GregT7/NetraPi/project_management/specs/test_matrix.xlsx

Sheet: tp
test_number | test_name | description | status
TP-01 | Budget compliance check | Verifies the total NetraPi system cost remains within the allowed budget. | PASS
TP-02 | Picam smoke test | Verifies the Raspberry Pi detects the camera and can display clear live output. | PASS
TP-03 | Portable-battery-only power verification | Verifies the Raspberry Pi can boot and operate using only the portable battery. | PASS
TP-04 | Camera mounting verification | Verifies the camera is mounted securely and provides a stable, usable forward-facing view during driving. | PASS
TP-05 | Vehicle compatibility inspection | Verifies the planned hardware can be installed and operated within a 2010 Mazda3 sedan. | PASS
TP-06 | Safety and legality review | Verifies the installed system does not obviously violate safety or driving constraints. | PASS
TP-07 | Reversible removal verification | Verifies the Pi, TPU, and battery can be removed and reinstalled without permanent modification or damage. | PASS
TP-08 | Three-hour continuous recording to memory | Verifies the system continuously records and writes footage to memory for at least 3 hours. | PASS
TP-09 | Texas-summer supervised operation check | Verifies the system can operate under typical Texas summer temperatures with supervision. | PASS
TP-10 | Coral TPU smoke test | Verifies the Coral USB TPU is detected and usable on the Raspberry Pi. | PASS
TP-11 | AI inference smoke test (camera + TPU) | Verifies real-time inference runs on live camera feed with object detection output. | PASS
TP-11.5 | Live inference pipeline throughput and latency benchmark | Measures the performance of the live camera-to-TPU inference pipeline, including effective FPS, processing latency, and identification of system bottlenecks. | PASS
TP-12 | Detection loop real-time operation | Verifies continuous inference execution without crashes or stalls. | PASS
TP-13 | Capture configuration validation | Verifies resolution, frame rate, and buffer duration are configurable and applied correctly. | PASS
TP-14 | Rolling buffer and event clip extraction verification | Verifies rolling buffer and event-triggered clip generation produce correct pre/post coverage. | PASS
TP-15 | Speaker module feedback verification | Verifies the speaker module produces audible feedback suitable for in-vehicle use. | PASS
TP-16 | Event clip pipeline and project layout | Verifies the event/clip pipeline is documented and the repo layout matches the planned `src/` structure for the edge capture path (no DB or cloud wiring required). | PASS
TP-17 | Config loading unit verification | Verifies JSON config files load into typed config objects used by capture and detector modules. | PASS
TP-18 | Detector data model and unit tests | Verifies `Classification`, `FrameRecord`, `FrameBuffer`, and `DetectorConfig` behave per the pipeline design. | PASS
TP-19 | Detector inference unit tests (mocked TPU) | Verifies `Detector.classify(raw)` wiring with mocked `_invoke` (no Coral required). | PASS
TP-20 | Detector on-device smoke | Verifies `load()`, `verify_tpu()`, and one real `classify(raw)` on the Pi with Coral attached. | PASS
TP-21 | RecordingManager capture unit tests | Verifies capture-related classes (`Camera`, `FrameProcessor`, `FrameRecord`, `FrameBuffer`, `Recorder`, `ClipPackage`, `PreviewUI`, etc.) pass unit tests and live under the planned `src/` layout. | PASS
TP-22 | RecordingManager idle run loop integration | Verifies `run_loop()` idle path: camera → `FrameRecord` → `pre_buffer.push` with stub config and without requiring unsafe-event logic. | PASS
TP-23 | RecordingManager clip-active path and MP4 output | Verifies `clip_active` post-roll, `ClipPackage.build`, and `Recorder.write_clip` produce a playable MP4 from buffer `display` frames. | PASS
TP-24 | RecordingManager Ctrl+C and preview controls | Verifies clean shutdown on Ctrl+C and preview show/hide per config. | PASS
AT-2.1 | Recorder write failure and recovery | Verifies `RecordingManager` handles `Recorder.write_clip(...)` failures safely (writer open fail, mid-write exception, output path issue) and recovers for subsequent clips. | PASS
AT-2.2 | Event gate policy matrix (unsafe vs safe) | Verifies clip-start policy exactly matches design: unsafe events always record; safe events record only when `record_safe_events = true`. | PASS
AT-2.3 | Post-roll completion boundary precision | Verifies post-roll finalization gate is correct at threshold boundaries (`min_post_frames_for_fps`) and avoids off-by-one behavior. | PASS
AT-2.4 | Deterministic preview-to-file parity | Verifies `PreviewUI` and saved MP4 carry the same processed `display` frames using deterministic frame markers (not subjective visual comparison). | PASS
AT-2.5 | Long-run multi-cycle stability and resource hygiene | Verifies repeated `idle -> clip_active -> idle` cycles remain stable over an extended run without state/resource leakage. | PASS
TP-25 | Stop-sign event classification (recorded clips) | Verifies classification on ~100 labeled clips (~25 each: rolling stop, run-through, complete stop, no event); overall accuracy ≥ 75%; per-category counts recorded. | PASS
TP-26 | Unsafe event clip extraction for stop-sign violation | Verifies an evidence clip is saved for an unsafe stop-sign event (rolling stop or run-through) and includes the encounter footage. | PASS
TP-27 | Audible feedback on unsafe stop-sign event | Verifies audible feedback for rolling-stop and run-through events within 10 seconds of detection. | PASS
TP-28 | Stop-sign beep test (in-vehicle) | Verifies in-car speaker beeps (3× 1.5s) when approaching three different stop signs. | PASS
AT-3.1 | Buzzer secured in Pi enclosure (GPIO wiring) | Buzzer mounted and wired safely in the Pi enclosure (BCM 18). | PASS
AT-3.3 | Continuous approach live benchmark (Pi FPS + overlay) | Live approach path meets FPS/latency targets; approach visible on HDMI. | PASS
AT-3.4 | Live approach + motion + classification bench (Pi) | Pi soak: approach + 5s motion + two-stage kNN; one cycle per maneuver; timing/FPS OK. | PASS
TP-29 | Local database schema validation | Verifies the local SQLite schema is structured correctly for event metadata storage (no upload-queue tables). | PASS
TP-30 | Local database write/read smoke test | Verifies the application can persist and retrieve dummy event records from SQLite. | PASS
TP-31 | Event metadata local storage verification | Verifies unsafe stop-sign events are stored in SQLite with required metadata. | PASS
TP-32 | Private S3 bucket provisioning | Verifies a private AWS S3 bucket exists for NetraPi media. | PASS
TP-33 | Supabase project and Postgres connectivity | Verifies the Supabase (Postgres) project exists and accepts connections from the development machine (admin / psql / SQL editor). This is not the FastAPI app connecting. | PASS
TP-34 | Local FastAPI smoke insert (driving-session) | Verifies a local FastAPI app (uvicorn, not Docker) can POST /api/netrapi/driving-session and insert one SQLite row. JSON only — no file body. | PASS
TP-35 | Local FastAPI health | Verifies GET /health on the local uvicorn app returns liveness and a UTC timestamp. No API key. | PASS
TP-36 | Local FastAPI smoke insert (driving-event) | Verifies POST /api/netrapi/driving-event on local uvicorn inserts one event plus nested children into SQLite (clip local flags, auto classification). JSON only — no file body. | PASS
TP-37 | Local backend boots via Docker Compose | Verifies the local FastAPI backend starts from the repo’s local Docker / Compose setup. | PASS
TP-38 | Local backend can reach S3 | Verifies the local backend process is configured with AWS credentials and can write a small test object to the private bucket. | PASS
TP-39 | Local backend can reach Supabase | Verifies the local backend can open a Postgres session to Supabase using its configured credentials. | PASS
TP-40 | Cloud metadata schema deployment | Verifies the event-metadata schema is applied to Supabase Postgres from the running local backend. | PASS
TP-41 | Trip-segment local insert | Verifies full-session trip recording writes at least one trip_segment row with a local MP4 path after the loop stops. | PASS
TP-42 | Edge API-key authentication | Verifies the local backend authenticates edge clients with an API key and rejects unauthenticated requests. | PASS
TP-43 | s3-upload-url issuance and edge PUT | Verifies POST /api/netrapi/s3-upload-url (JSON only) returns a time-limited S3 PUT URL and object key and the client PUTs bytes to S3 not to FastAPI. | PASS
TP-44 | Stable S3 object key generation | Verifies the backend assigns consistent deterministic object keys. | PASS
TP-45 | driving-event persist to Supabase | Verifies authenticated POST /api/netrapi/driving-event writes one event plus nested children to Postgres. JSON only. Cloud counterpart of TP-36. | PASS
TP-46 | Private object access via signed GET | Ensures uploaded objects are not public and are reachable via backend-issued signed GET URLs (POST /api/netrapi/s3-download-url). | PASS
TP-47 | confirm-s3-upload links S3 object to Postgres | Verifies POST /api/netrapi/confirm-s3-upload (JSON only) sets s3_key / s3_stored after the edge PUT in TP-43. | PASS
TP-48 | Presigned upload over hotspot/mobile data | Verifies an edge client can complete a backend-orchestrated upload over cellular/hotspot connectivity. | PASS
TP-49 | Local end-to-end event persistence via backend | Verifies a local event (SQLite plus clip) uploads one-at-a-time through the local backend into S3 and Postgres. | PASS
TP-50 | Backend Docker image build | Verifies the backend Docker image builds and runs locally from the production Dockerfile. | PASS
TP-51 | Backend deployment to hosting environment | Verifies the backend deploys successfully to the target host (e.g., Render). | PASS
TP-52 | Deployed backend API-key authentication | Verifies the deployed backend authenticates edge clients with an API key, rejects unauthenticated requests, and still accepts a valid key (same contract as local TP-42). | PASS
TP-53 | Unsafe event to cloud via deployed backend | Verifies an unsafe stop-sign event is detected on the edge, alerts locally, and uploads through the deployed backend to S3 + Postgres. | PASS
TP-54 | Cross-layer metadata consistency | Verifies event identity and fields stay consistent across the TP-53 SQLite artifact (session / event / clip / trip / s3_key) after a successful CloudIngest confirm (no frontend; no backend .env on the Pi). | PASS
TP-55 | Restart recovery then upload | Verifies local event data survives an edge restart and can upload later via the deployed backend. | PASS
TP-56 | Deployed system smoke (API/cloud evidence) | Verifies a minimal real-world flow from detection through deployed-backend upload, confirmed without a frontend. | PASS
AT-7.1 | Mocked Pi pipeline to deployed cloud | Verifies the real edge pipeline (build_pipeline → RecordingManager.run_loop → LocalStore persist → CloudIngest) can upload one unsafe event through Render to S3 + Postgres when the camera and EventManager are mocked. Unlike TP-53/TP-56, this does not seed rows or call ingest APIs from the harness. | PASS
AT-7.2 | Camera + SPACE + stubbed events to deployed cloud | Dry-run before live AT-7.3. Same three SPACE-armed phases as TP-28 / AT-7.3 (complete stop → rolling stop → run-through) with real camera + preview, but EventManager is stubbed so SPACE injects the intended event. Persist and upload still go through RecordingManager / LocalStore / CloudIngest. | PASS
AT-7.3 | In-car three-maneuver E2E to deployed cloud | Full in-vehicle E2E on the fully integrated edge pipeline (real camera, Detector, EventManager, Buzzer, Recorder, LocalStore, CloudIngest): one complete stop, one rolling stop, and one run-through, then confirm unsafe events in SQLite, S3, Postgres, and Render logs. Same SPACE-armed phases as TP-28; cloud path is the production ingest, not a seed harness. | PASS
TP-57 | TPU smoke abort | Failed Coral TFLite dummy invoke aborts main.py before capture (exit 1). | PASS
TP-58 | Offline when Wi-Fi is missing or internet fails | No association is informational offline; associated-but-no-internet is loud offline; both still start capture. | PASS
TP-59 | Authenticated /ready (Postgres + S3) | GET /api/netrapi/ready requires API key and checks SELECT 1 plus S3 HeadBucket; GET /health stays cheap liveness. | PASS
TP-60 | Online boot and keep-alive drop to offline | Online when internet plus /health plus /ready succeed; three keep-alive failures drop to offline for the rest of the process. | PASS
TP-61 | Drain clips trips or both | --drain-trips requires clips|trips|both; wakes Render via /health then uploads selected pending media. | PASS
TP-62 | Health settings snapshot | health.json is loaded at runtime and snapshotted as health_config (Alembic 0004) in the master-config fingerprint. | PASS
TP-63 | Public confirmed-clip list | GET /api/public/clips returns confirmed public_visible clips without an API key; ingest routes stay keyed. | PASS
TP-64 | Public mint vs ingest mint | Public mint is a 2-minute GET with no device API key; keyed ingest mint stays 401 without the key. | PASS
TP-65 | Public mint limits | 21st concurrent live GET is 429; 11th mint from one IP in 60s is 429. | PASS
TP-66 | Try it out browse and play | Try-it-out loads real-world API clips, shows Field/FP/Calibrated counts, mints on click, Detailed Analysis default. | PASS
TP-67 | Local clip directory with playback JSON | Event clip writes clip.mp4 plus areas.json, motion.json, and transitions.json in one local directory. | PASS
TP-68 | Clip upload URL issues four objects | s3-upload-url for a clip returns clip.mp4 plus PUTs for the three sidecar JSON objects. | PASS
TP-69 | Confirm requires video and sidecar objects | confirm-s3-upload HEADs all four objects; missing sidecar is 400. | PASS
TP-70 | Public mint inlines sidecar JSON | Public mint returns sidecar JSON without extra live URL slots; live_urls increases by 1. | PASS
TP-71 | Clip flags and live Results accuracy | flag_def/clip_flag; public list flags; Field vs Calibrated Accuracy; non-real_world clips are not public. | PASS
TP-72 | GitHub Actions lint, unit tests, and gated deploy | CI lint/unit/build on updates; Render+Vercel deploy on main only after green; health curls must pass. | PASS
TP-73 | systemd manual start and stop | Edge starts and stops as netrapi-edge.service by hand and is not enabled on boot.
TP-74 | 10-hour fixed-config collection and labels | ≥10 hours driving with frozen config; drain trips and clips to S3; manual labels for Field/Calibrated Accuracy.

Sheet: evidence
evidence_id | test_number | evidence_type | evidence_url | notes
1 | TP-02 | video | https://www.youtube.com/watch?v=-5VuUhmwbzs | User-provided YouTube evidence link for Picam smoke test
2 | TP-03 | video | https://youtu.be/R1Axi_fZByw
3 | TP-10 | video | https://youtu.be/2TyjnwohFwI
4 | TP-10 | video | https://youtu.be/iin7XSLdfmM
5 | TP-12 | logs | https://drive.google.com/drive/folders/1ha0Pd6iwO-m7OFLlRQCs0ZM-E614eOiR?usp=drive_link
6 | TP-11 | video | https://youtu.be/h4BOTX9eofg
7 | TP-11.5 | video | https://youtu.be/zWOMBMkm1cA
8 | TP-12 | logs | https://drive.google.com/drive/folders/1ha0Pd6iwO-m7OFLlRQCs0ZM-E614eOiR
9 | TP-13 | video | https://youtu.be/joZcwk1W1W0
10 | TP-13 | logs | https://drive.google.com/drive/folders/1PHiny_EQ_2M6K0LmAgpXgGuW0FzlqmN6
11 | TP-14 | video | https://youtu.be/S2jUfkglFMA
12 | TP-14 | files | https://drive.google.com/drive/folders/1IVgWyRJZYwZcIyBNpHSB5XdV-ARYEYyn
13 | TP-15 | video | https://youtu.be/DtoR-teizX0
14 | TP-04 | video | https://www.youtube.com/watch?v=560_ZivC_qQ
15 | TP-15 | video | https://youtu.be/sfeg-gEdRMc
16 | TP-05 | video | https://youtu.be/QwmW4sI85JM
17 | TP-06 | video | https://youtu.be/duzUvhIk4Pg
18 | TP-07 | video | https://youtu.be/LwzJlO6Gu6w
19 | TP-01 | excel | https://drive.google.com/drive/folders/1YolW1nTg-rEjDPZTnhUKF6_n0XvjO1hy
20 | TP-08 | logs | https://drive.google.com/drive/folders/1W_vF1XtQUT1lksW65h6gn6InxTWftMUu
21 | TP-08 | video | https://youtu.be/T6wfl0Q8mxU
22 | TP-09 | logs | https://drive.google.com/drive/folders/1vrvyoE124rbHkEHGdCiSdVmXNGFAQWLk
23 | TP-09 | video | https://youtu.be/E2MdRicHgr4
24 | TP-16 | files | https://github.com/GregT7/NetraPi/blob/main/project_management/diagrams/event_clip_pipeline.md
25 | TP-16 | files | https://github.com/GregT7/NetraPi/blob/main/project_management/diagrams/directory_tree.md
26 | TP-17 | photo | https://drive.google.com/drive/folders/1SVD47iArKHrq7TeCZprKcEFciZo6ZAPF
27 | TP-17 | files | https://github.com/GregT7/NetraPi/tree/main/src/tests/unit/edge/config
28 | TP-18 | photo | https://drive.google.com/drive/folders/1uDxutfOd4gLpaEC6vgzj5kx7HPf_qqtV
29 | TP-18 | files | https://github.com/GregT7/NetraPi/tree/main/src/tests/unit/edge/netrapi/buffer
30 | TP-18 | files | https://github.com/GregT7/NetraPi/tree/main/src/tests/unit/edge/netrapi/detection
31 | TP-19 | files | https://drive.google.com/drive/folders/1phl3is13xoqX30jkrS9yDSBdeskKDdBT
32 | TP-19 | files | https://github.com/GregT7/NetraPi/tree/main/src/tests/unit/edge/netrapi/detection
33 | TP-19 | files | https://github.com/GregT7/NetraPi/blob/main/src/tests/unit/edge/netrapi/recording/test_recording_manager.py
34 | TP-20 | video | https://youtu.be/OwMxtak17Jc
35 | TP-20 | files | https://drive.google.com/drive/folders/1PnGZOJxcfH8uEJteyx-yiuWnEM9bM6Za
36 | TP-21 | photo | https://drive.google.com/drive/folders/1JaY3_6Ci7zWddcsMYAAbsQBx1hTN3SLo
37 | TP-21 | files | https://github.com/GregT7/NetraPi/tree/main/src/tests/unit/edge/netrapi/buffer
38 | TP-21 | files | https://github.com/GregT7/NetraPi/tree/main/src/tests/unit/edge/netrapi/capture
39 | TP-21 | files | https://github.com/GregT7/NetraPi/blob/main/src/tests/unit/edge/netrapi/recording/test_recorder.py
40 | TP-21 | files | https://github.com/GregT7/NetraPi/blob/main/src/tests/unit/edge/netrapi/recording/test_clip_package.py
41 | TP-21 | files | https://github.com/GregT7/NetraPi/blob/main/src/tests/unit/edge/netrapi/recording/test_recording_manager.py
42 | TP-22 | files | https://drive.google.com/drive/folders/1eWlZAQpwSfV7a8UnPKqtzIloqkbP3wKf
43 | TP-22 | video | https://youtu.be/uHPcOQ18HQg
44 | TP-23 | video | https://youtu.be/E-vNfDcQLzE
45 | AT-2.5 | files | https://drive.google.com/drive/folders/1qOUVhqMvfYs_HeHORKjGaS_m8wntXcf7
46 | TP-24 | files | https://drive.google.com/drive/folders/12QTc4U_krTKWBVjtYGbmb8TNMe_51o6y
47 | AT-2.1 | files | https://drive.google.com/drive/folders/1VoTWCFGyhRdzUP_-B4JyA3Gq8UurDSj1
48 | AT-2.3 | files | https://drive.google.com/drive/folders/1fdIt5WgfajlHIvtyxhIqP3eYavRHSDos
49 | AT-2.4 | files | https://drive.google.com/drive/folders/17CdyNwHGwQe7pYjzFvKOQ-9AiMas1V_N
50 | AT-2.5 | files | https://drive.google.com/drive/folders/1qOUVhqMvfYs_HeHORKjGaS_m8wntXcf7
51 | AT-2.4 | video | https://youtu.be/5snqu62aBeA
52 | AT-2.5 | video | https://youtu.be/nDdzcWqfG3s
53 | AT-2.3 | video | https://youtu.be/GlS2PfqYLVo
54 | AT-2.2 | video | https://youtu.be/1yGiLqSesYA
55 | AT-2.1 | video | https://youtu.be/zqGMKMnmU9I
56 | TP-24 | video | https://youtu.be/_asbeM2JNWs
57 | AT-3.3 | video | https://youtu.be/nRbR8uva_wg
58 | AT-3.4 | video | https://youtu.be/BHpvCfraFlw
59 | TP-25 | files | https://docs.google.com/spreadsheets/d/1mFMXTRxfy0TCIs2vldU8GiSohJhjfY30/edit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
60 | TP-26 | video | https://youtu.be/1xkTqvEPAb4
61 | AT-3.4 | video | https://youtu.be/Orc6_g71sUM
62 | AT-3.1 | video | https://youtu.be/a3k-1uSnozI
63 | TP-15 | video | https://youtu.be/zDOH2GECahk
64 | TP-27 | video | https://youtu.be/Q_9Z74owBv8
65 | TP-28 | video | https://youtu.be/IT_ykP0Xb3I
66 | TP-29 | files | https://drive.google.com/drive/folders/1LFZ52JmMPF5uLb3dULrw7zhsWqxZ1jAN
67 | TP-30 | video | https://youtu.be/jg7FgDR0oAE
68 | TP-31 | video | https://youtu.be/M78sSDXlycc
69 | TP-32 | image | https://drive.google.com/drive/folders/1e6rSPmZ-qy5nWpntsSQftYKHDWPn8BbW
70 | TP-33 | files | https://drive.google.com/drive/folders/1z8qlavdIHWcaSoXJPDzINBx5NtD9WUa5
71 | TP-34 | files | https://drive.google.com/drive/folders/1EWViKnnlWnC2Zot-RRf1O8wTUSNBGYkE
72 | TP-35 | files | https://drive.google.com/drive/folders/1D6qtMUrYtRJmLQVm_B5WT-HNuJZGmOjl
73 | TP-36 | files | https://drive.google.com/drive/folders/1zDdyTawXSt8U7TMqV2cNbHTGg6dikERL
74 | TP-37 | files | https://drive.google.com/drive/folders/1KciBAz28NOFzD9vUF_ECv1K1va74sD-m
75 | TP-38 | files | https://drive.google.com/drive/folders/1O3JbI8--lNjJY9Rm-jYHLztAn9DVxq8K
76 | TP-39 | files | https://drive.google.com/drive/folders/1J5XoqlkMCCgFYjjFKbqlYl2xsIMAVRq2
77 | TP-40 | files | https://drive.google.com/drive/folders/1q3Ef3I3v8ZKLs0kSKW_EluyAvVHkECER
78 | TP-41 | files | https://drive.google.com/drive/folders/1XLbzDKWPG4iEhj7RlazVmDL5pvrk7Pf9
79 | TP-42 | files | https://drive.google.com/drive/folders/1zqrVgGtrc76QmKFAIL8sIY_fll4Wt1F-
80 | TP-43 | files | https://drive.google.com/drive/folders/1HP5cFozEKMbyEBHzSHwuinVOncUSUWJn
81 | TP-44 | files | https://drive.google.com/drive/folders/1SOAjhstdQm78f981-xgOKi3GEtTPVbUl
82 | TP-45 | files | https://drive.google.com/drive/folders/1gdr7XPsUSizf9HjnnPA4u9llTTdxjtwV
83 | TP-46 | files | https://drive.google.com/drive/folders/1rT6AYRTFZN3_c8Fm3EnyEsJM4v4zQmUB
84 | TP-47 | files | https://drive.google.com/drive/folders/17mVOh5k57LvYUe42WzBv7xIDxfKD95Mv
85 | TP-48 | files | https://drive.google.com/drive/folders/1p1LhCn_7pyC4k3icxougHnQCHvbGb93z
86 | TP-49 | files | https://drive.google.com/drive/folders/1TtmrqkeCX-MHqylO_8oxDEytVYTT2-_F
87 | TP-50 | files | https://drive.google.com/drive/folders/1M12N54PW3W1SZCFrWOywzrfizBVbFwXn
88 | TP-51 | files | https://drive.google.com/drive/folders/1Y53G10tKN7P9S5fbiNpwCOBL7GUuclUR
89 | TP-52 | files | https://drive.google.com/drive/folders/1Gk1KpAh7Ve2tQA4-nxxk1PYEA4P13uV-
90 | TP-53 | files | https://drive.google.com/drive/folders/1tOpxm7QzVw5PPGDlulU8dH0pqKVqKwFw
91 | TP-54 | files | https://drive.google.com/drive/folders/10wl41bJjyDcLUnV56kaSiX_rMDBguKpz
92 | TP-55 | files | https://drive.google.com/drive/folders/1iPJKhV6H8xP3rSgMR92JacJ-HCrgJ-B0
93 | TP-56 | files | https://drive.google.com/drive/folders/1HOxp1GtldOPPCJWeUIFUN1_LvhgqESOD
94 | AT-7.1 | files | https://drive.google.com/drive/folders/1XeGmkE_QONBqETsFdkrhBAeqoMk35NyG
95 | AT-7.2 | files | https://drive.google.com/drive/folders/1-kKJqIWDCmMsQB6fLZHJIlA7AZRLZt1J
96 | AT-7.3 | test
97 | TP-63 | test | src/tests/unit/backend/app/routes/test_public_clip.py
98 | TP-64 | test | src/tests/unit/backend/app/routes/test_public_clip.py
99 | TP-65 | test | src/tests/unit/backend/app/routes/test_public_clip.py
100 | TP-66 | test | src/tests/unit/frontend/src/TryItOut.test.tsx
101 | TP-67 | test | src/tests/unit/edge/netrapi/recording/test_playback_json.py
102 | TP-68 | test | src/tests/unit/backend/app/routes/test_s3_upload.py
103 | TP-69 | test | src/tests/unit/backend/app/routes/test_s3_upload.py
104 | TP-70 | test | src/tests/unit/backend/app/routes/test_public_clip.py
105 | TP-71 | test | src/tests/unit/frontend/src/App.test.tsx
106 | TP-72 | test | .github/workflows/ci.yml
107 | TP-73 | file | src/main/edge/netrapi-edge.service
108 | TP-73
109 | TP-74
